ModInFrance/PCE-Ribbon-Cable-Replacement/images/1 (4).jpg

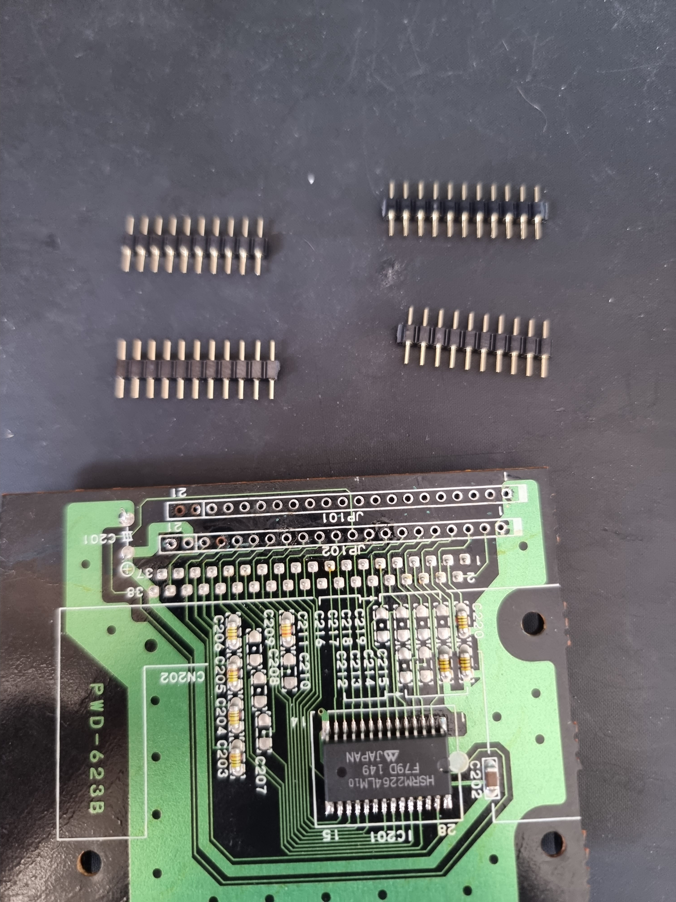
images/1 (4).jpg
