ModInFrance/PCE-Ribbon-Cable-Replacement/images/1 (12).jpg

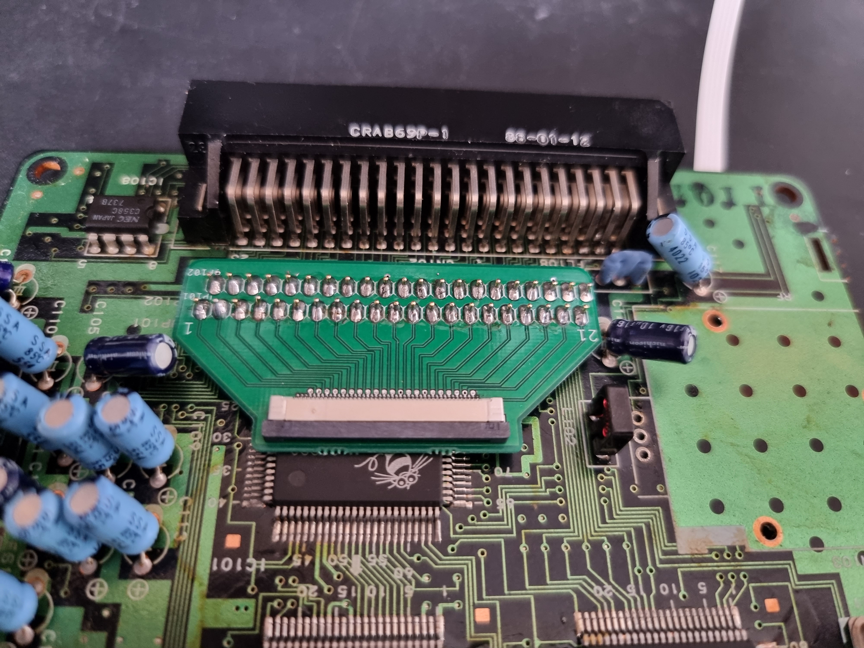
images/1 (12).jpg
