ModInFrance/PCE-Ribbon-Cable-Replacement/images/1 (14).jpg

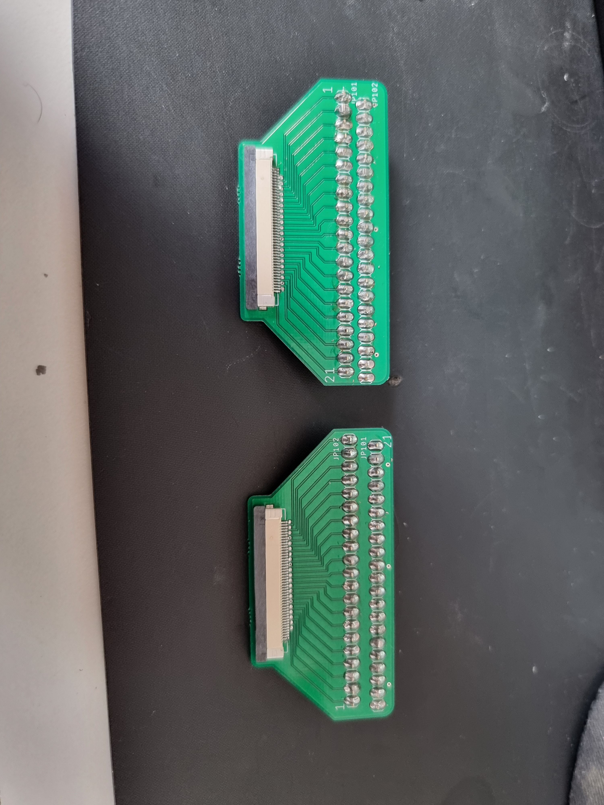
images/1 (14).jpg
